fckseng19/Buck-Boost_Converter/Buck-Boost/Simulaciones y cálculos/Gate Driver  OrCAD_Sim/GATEDRIVER.png

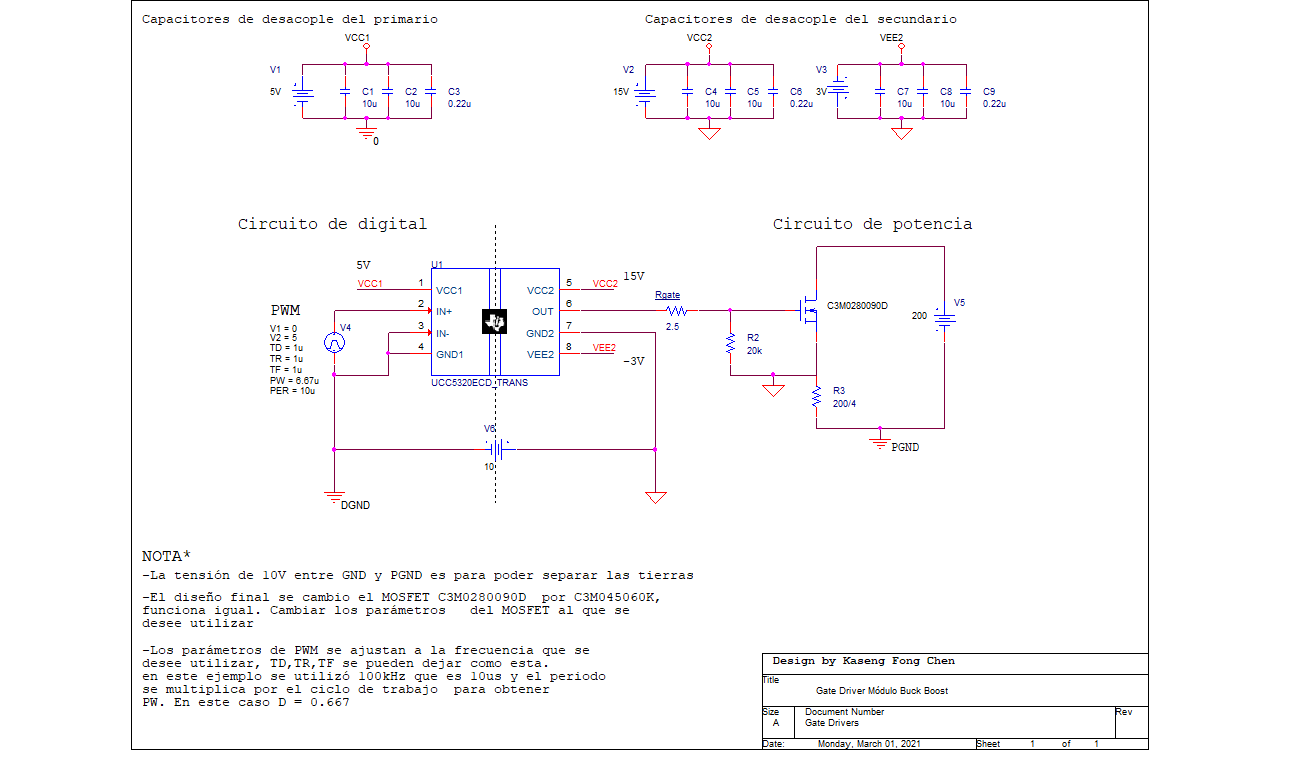
Buck-Boost/Simulaciones y cálculos/Gate Driver OrCAD_Sim/GATEDRIVER.png
